BCN3D/Arduino-Auto-Loader/img/IMG_1422.JPG

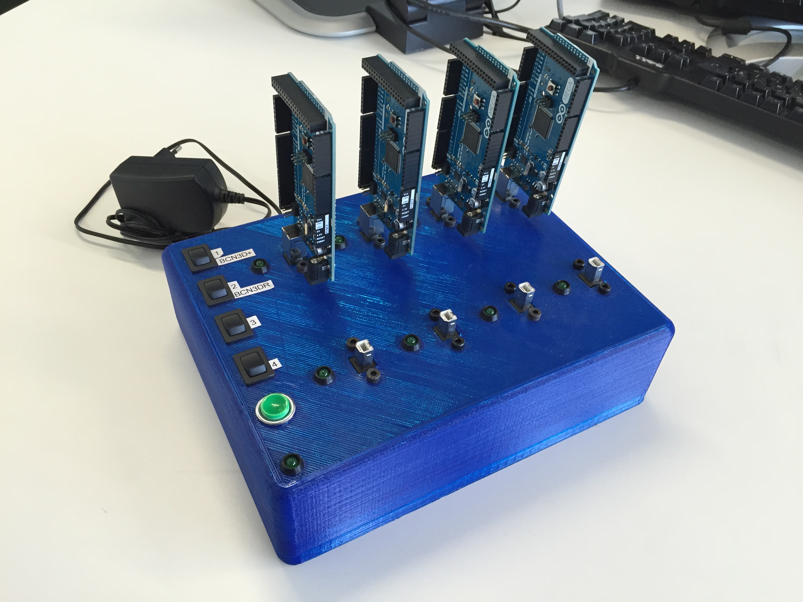
img/IMG_1422.JPG
