BCN3D/Arduino-Auto-Loader/img/IMG_1425.JPG

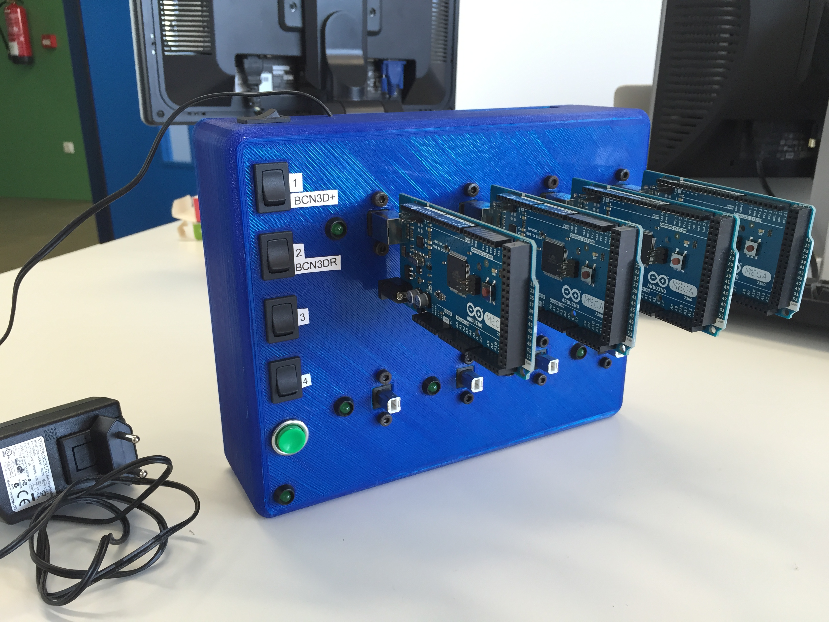
img/IMG_1425.JPG
